bitcores/pico-ps2famikb/usb2famikb-lib/usb2famikb.h

#pragma once

#ifdef __cplusplus
extern "C" {
#endif

void usb2famikb_init(uint nesin_gpio, uint nesoe1_gpio, uint nesoe2_gpio, uint kbout_gpio, uint kbmode);

void usb2famikb_putkb(const uint32_t nesout);

#ifdef __cplusplus
}
#endif
